PropNuts/wizardtracker-hardware/receiver.h

#ifndef RECEIVER_H
#define RECEIVER_H


#include <stdint.h>
#include "receiver_spi_driver.h"


class Receiver {
    public:
        Receiver(
            uint8_t spiClockPin,
            uint8_t spiDataPin,
            uint8_t spiSelectPin,
            uint8_t rssiPin
        );

        void updateRssi();
        void setFrequency(uint16_t frequency);

        uint16_t rssi;

    private:
        ReceiverSpiDriver driver;
        uint8_t rssiPin;
};


#endif
